coelacant1/BetaProtogen/Pictures/20210629_173443.jpg

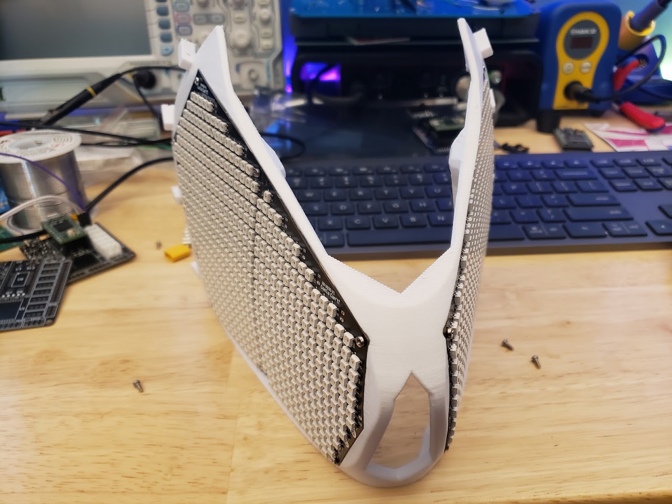
Pictures/20210629_173443.jpg
