coelacant1/BetaProtogen/Pictures/BottomLayer.png

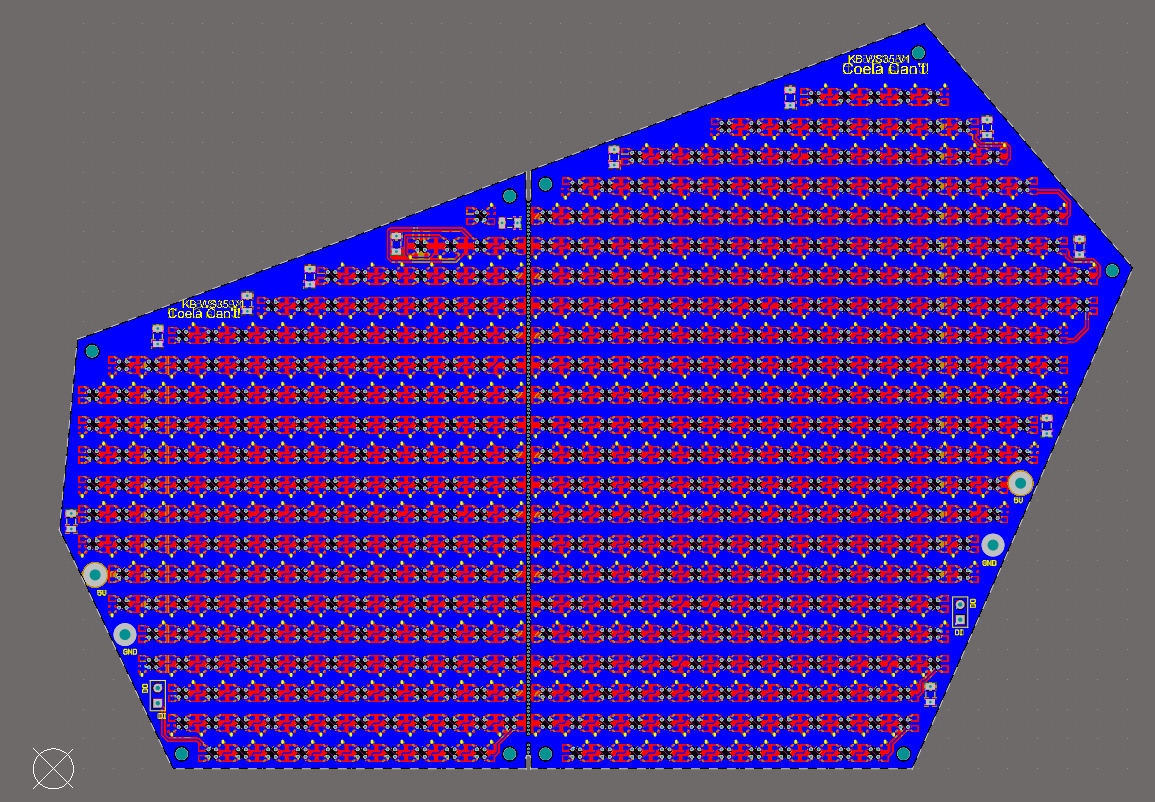
Pictures/BottomLayer.png
