coelacant1/BetaProtogen/Pictures/CoelaProtoPublicV1_WS35_blank.png

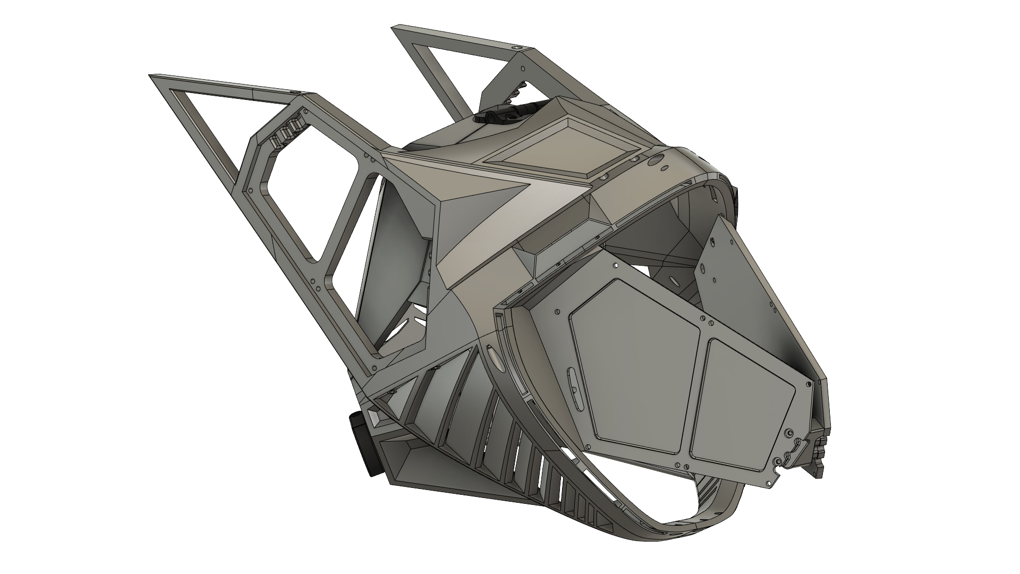
Pictures/CoelaProtoPublicV1_WS35_blank.png
