coelacant1/BetaProtogen/Pictures/CoelaProtoPublicV1_WS35_Bottom.png

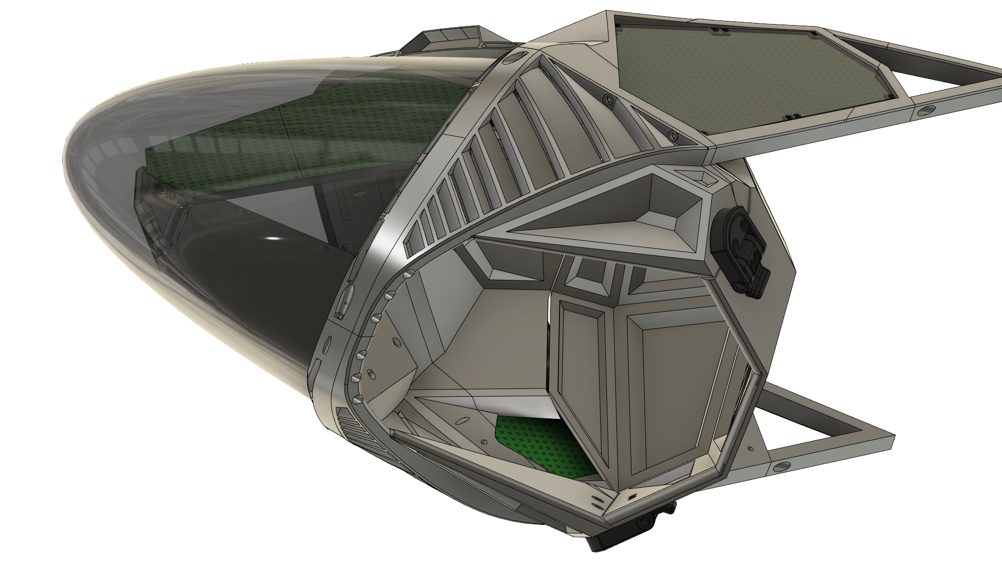
Pictures/CoelaProtoPublicV1_WS35_Bottom.png
