coelacant1/BetaProtogen/Pictures/CoelaProtoPublicV1_WS35_Full.png

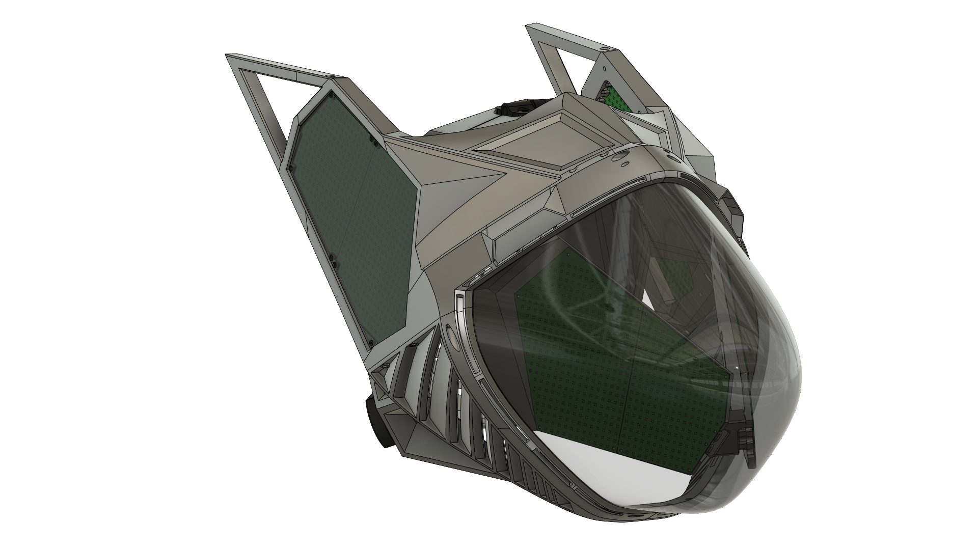
Pictures/CoelaProtoPublicV1_WS35_Full.png
