coelacant1/BetaProtogen/Pictures/CoelaProtoPublicV1_WS35_OpenBack.png

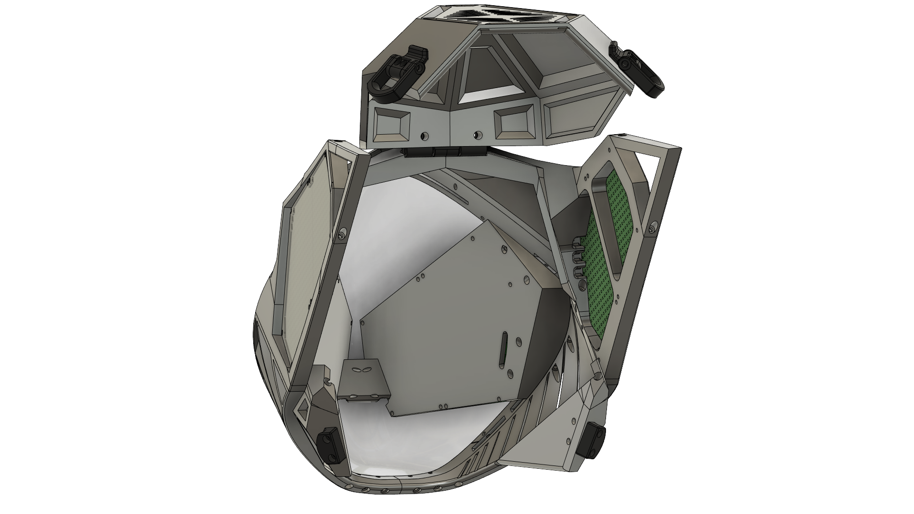
Pictures/CoelaProtoPublicV1_WS35_OpenBack.png
