coelacant1/BetaProtogen/Pictures/E_W8pO6XIAAdrPj.jpg

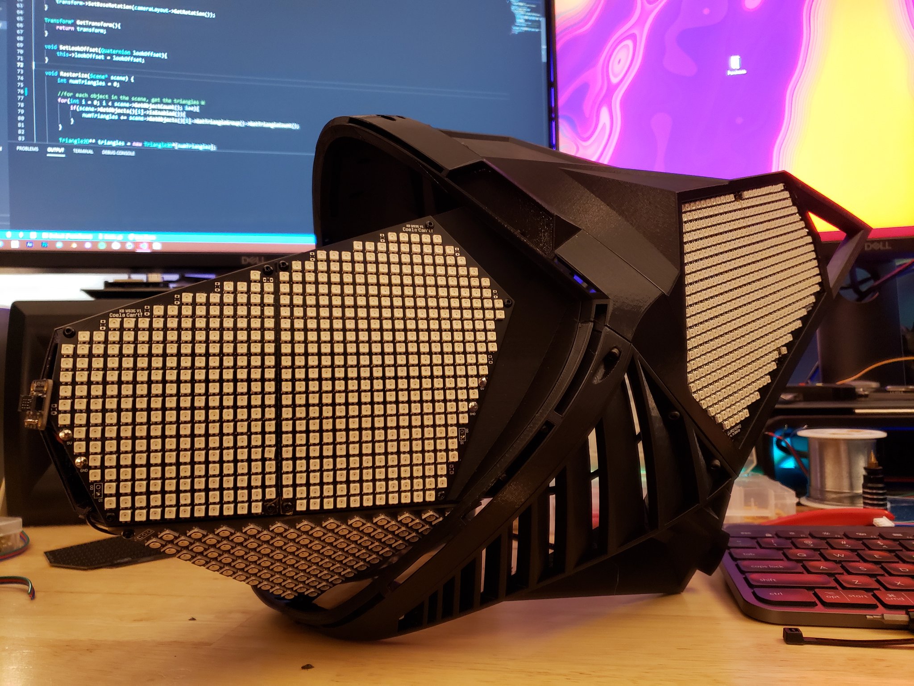
Pictures/E_W8pO6XIAAdrPj.jpg
