coelacant1/BetaProtogen/Pictures/FullHead.png

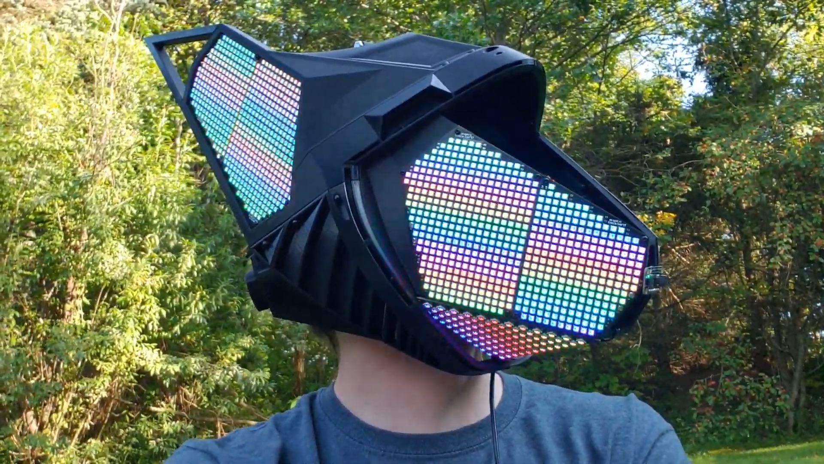
Pictures/FullHead.png
