coelacant1/BetaProtogen/Pictures/LED.png

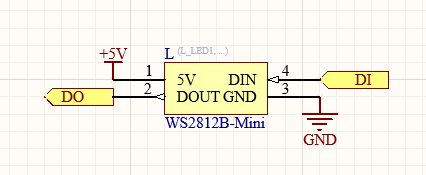
Pictures/LED.png
