coelacant1/BetaProtogen/Pictures/Thumbnail.png

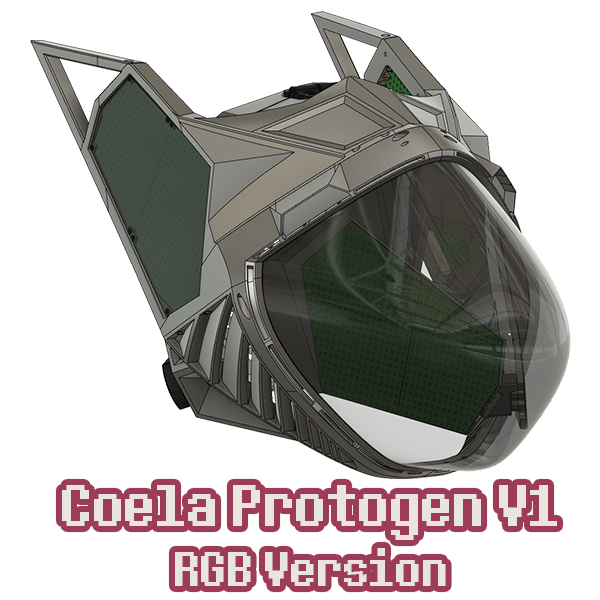
Pictures/Thumbnail.png
