coelacant1/BetaProtogen/Pictures/TopCopper.png

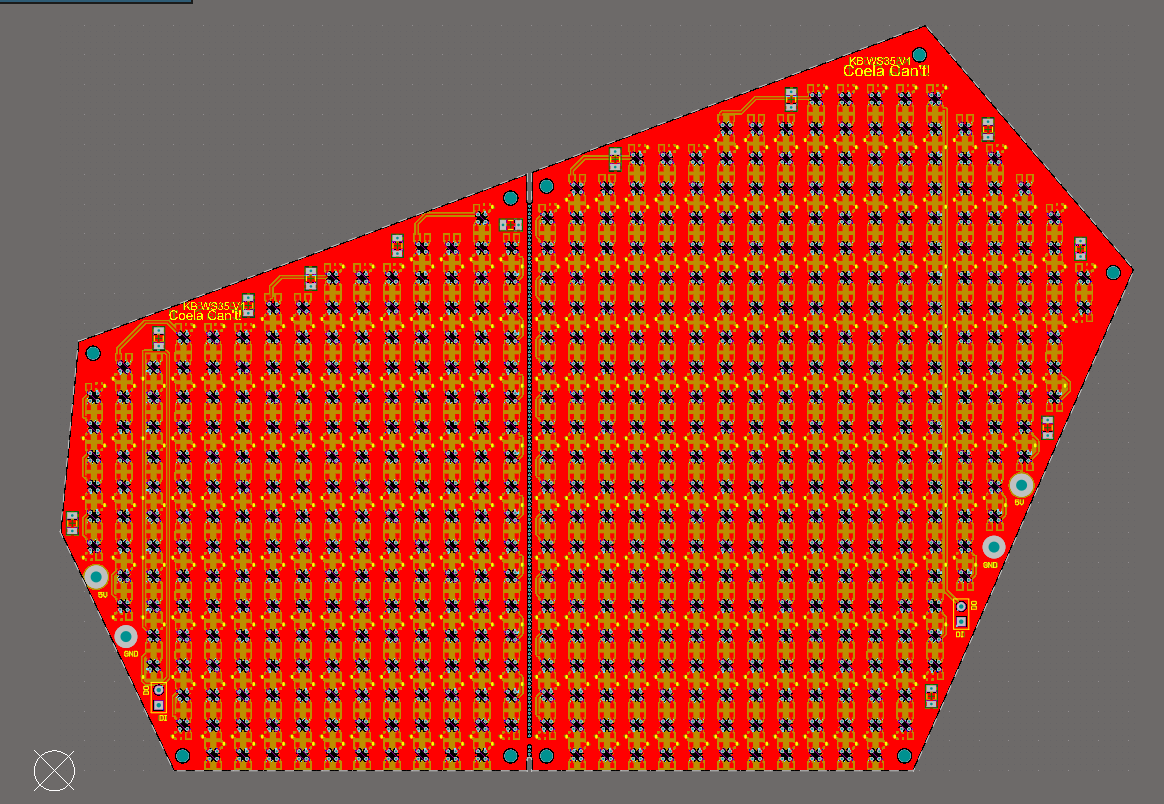
Pictures/TopCopper.png
