coelacant1/BetaProtogen/LED Mount WS35/WS35FlatMountRight_V1-0.stl

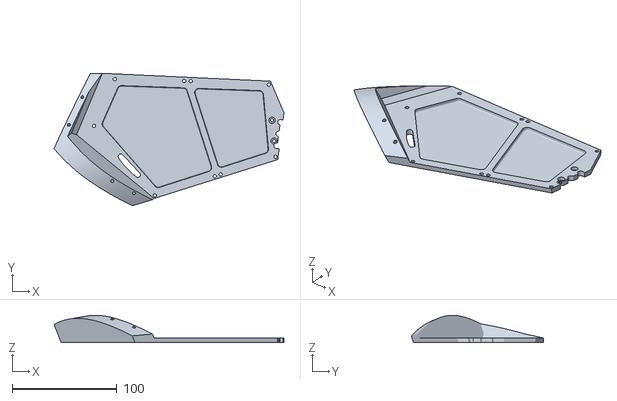
[picture p32: CAD file, 2023-06-26]
LED Mount WS35/WS35FlatMountRight_V1-0.stl
219.6 x 126.5 x 26.1
