coelacant1/BetaProtogen/Visor/Visor_V1-0.stl

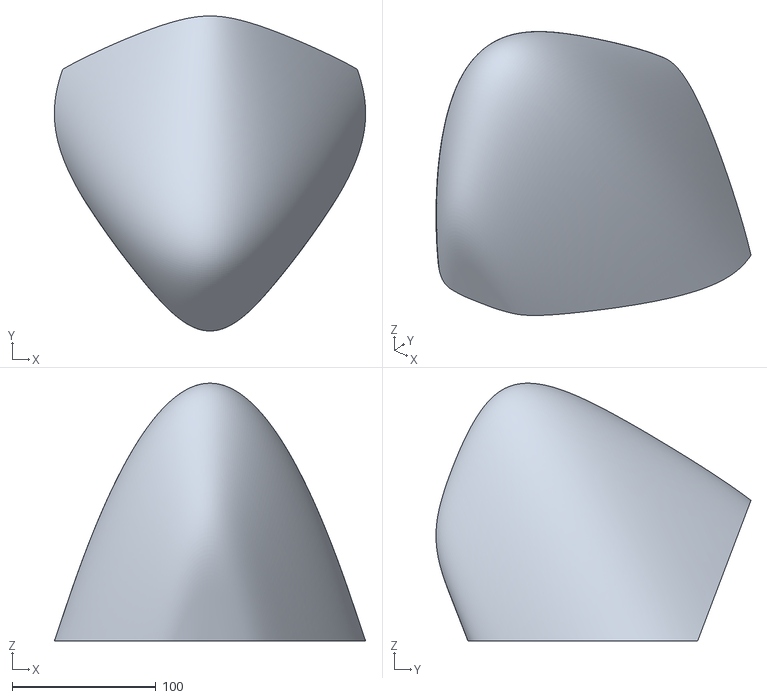
[picture p33: CAD file, 2023-06-26]
Visor/Visor_V1-0.stl
216.9 x 219.5 x 179.5
