coelacant1/BetaProtogen/VisorMount/BotVisorFrameMount_V1-0.stl

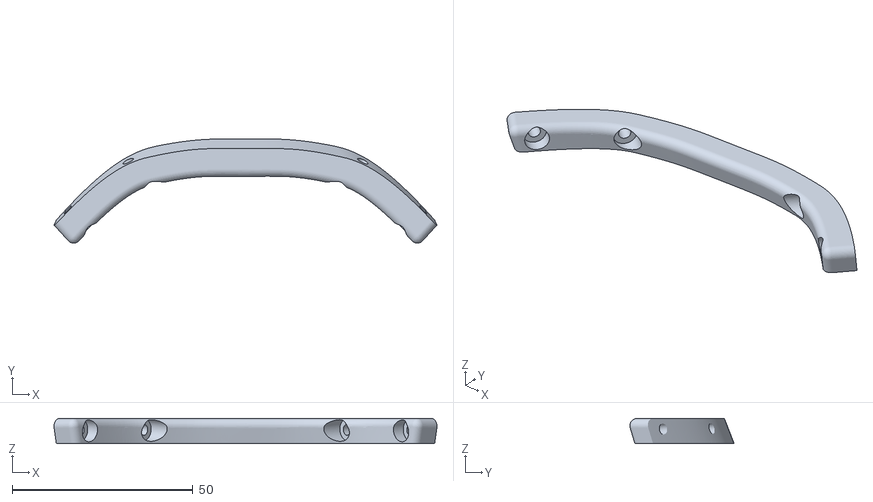
[picture p34: CAD file, 2023-06-26]
VisorMount/BotVisorFrameMount_V1-0.stl
106.0 x 28.9 x 6.94
