coelacant1/BetaProtogen/Frame/FrameForeheadL_V1-1.stl

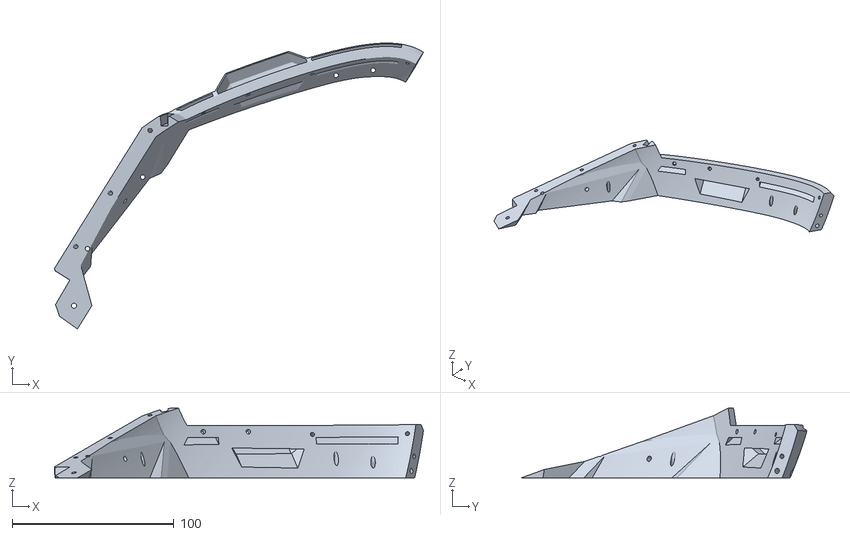
[picture p35: CAD file, 2023-06-26]
Frame/FrameForeheadL_V1-1.stl
228.0 x 176.6 x 43.2
