coelacant1/BetaProtogen/VisorMount/TopBackMagnet.stl

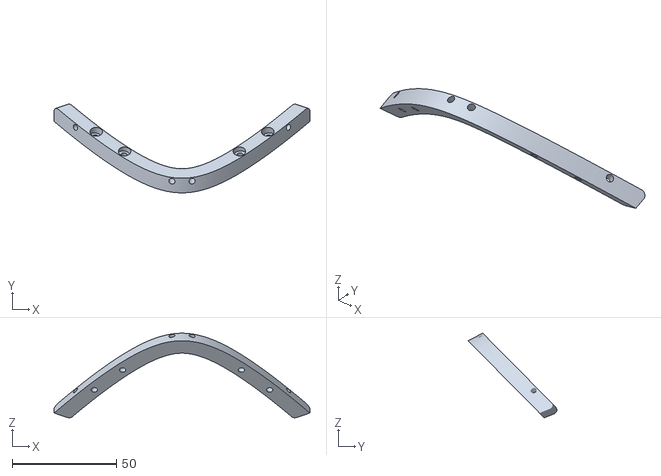
[picture p38: CAD file, 2023-06-26]
VisorMount/TopBackMagnet.stl
122.6 x 42.5 x 40.5
