coelacant1/BetaProtogen/Frame/FrameJawR_V1-1.stl

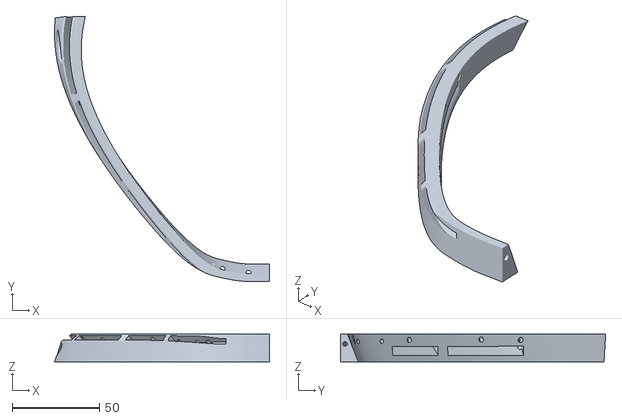
[picture p39: CAD file, 2023-06-26]
Frame/FrameJawR_V1-1.stl
123.0 x 151.8 x 15.8
