coelacant1/BetaProtogen/Latch/LatchRightMount_V1-0.stl

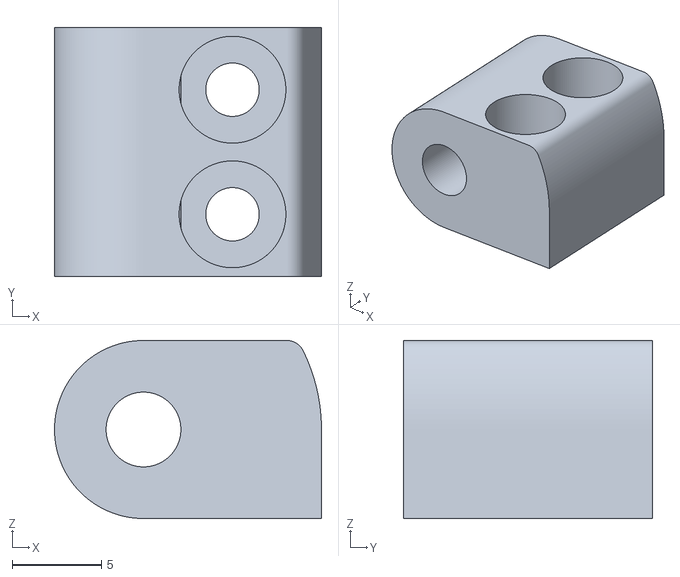
[picture p40: CAD file, 2023-06-26]
Latch/LatchRightMount_V1-0.stl
15.0 x 14.0 x 10.0
