coelacant1/BetaProtogen/LED Mount MAX7219/MAX7219BottomRight_V1-0.stl

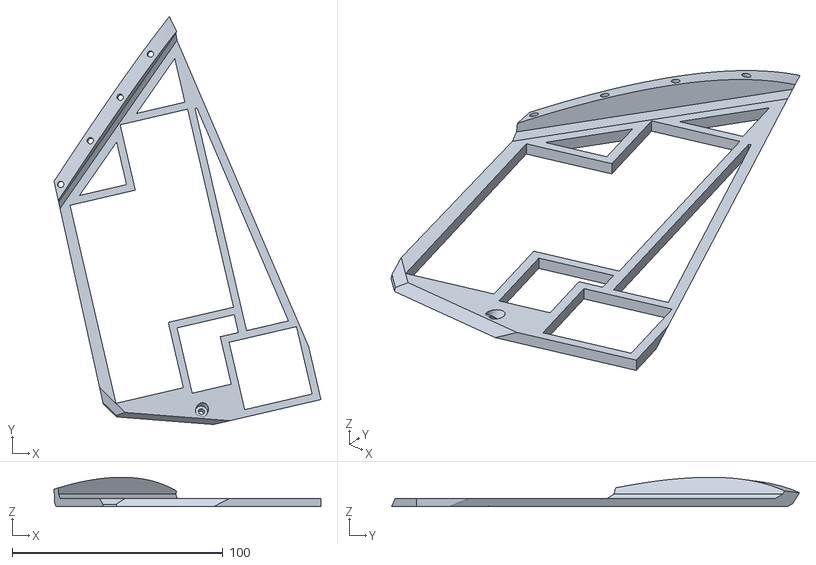
[picture p41: CAD file, 2023-06-26]
LED Mount MAX7219/MAX7219BottomRight_V1-0.stl
126.6 x 193.4 x 14.0
