coelacant1/BetaProtogen/LED Mount WS35/WS35BendMount_V1-0.stl

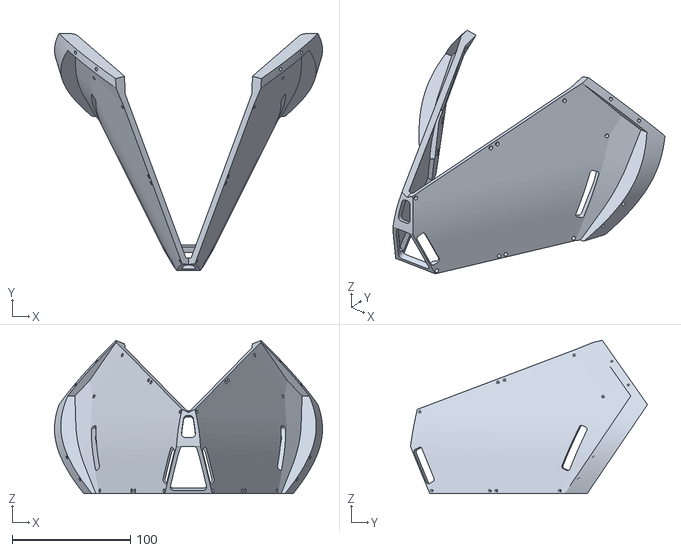
[picture p42: CAD file, 2023-06-26]
LED Mount WS35/WS35BendMount_V1-0.stl
226.4 x 200.2 x 129.4
