coelacant1/BetaProtogen/Visor/VisorCoverBottom_V1-0.stl

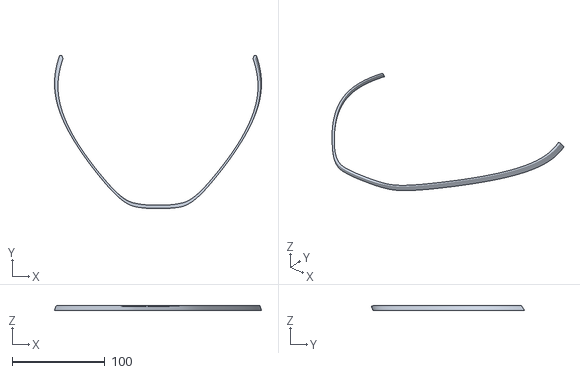
[picture p43: CAD file, 2023-06-26]
Visor/VisorCoverBottom_V1-0.stl
222.6 x 164.7 x 5.00
