coelacant1/BetaProtogen/VisorMount/TopVisorFrameMount_V1-0.stl

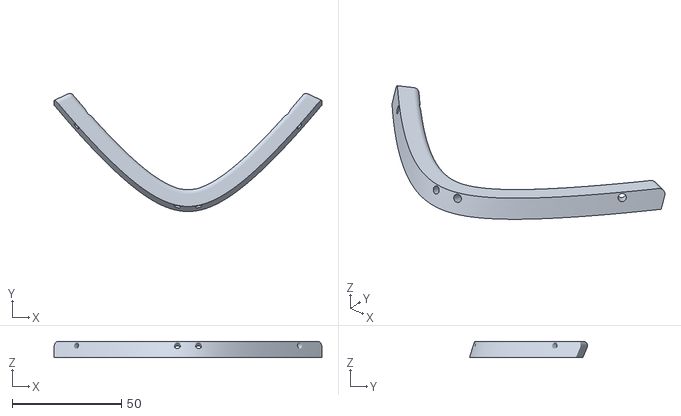
[picture p44: CAD file, 2023-06-26]
VisorMount/TopVisorFrameMount_V1-0.stl
122.6 x 54.0 x 7.54
