coelacant1/BetaProtogen/Frame/FrameForeheadR_V1-1.stl

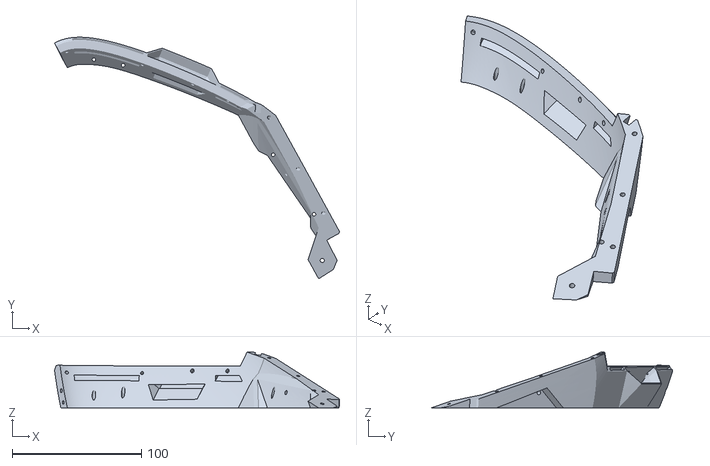
[picture p45: CAD file, 2023-06-26]
Frame/FrameForeheadR_V1-1.stl
220.4 x 186.8 x 43.2
