coelacant1/BetaProtogen/LED Mount MAX7219/MAX7219LEDConnector_V1-0.stl

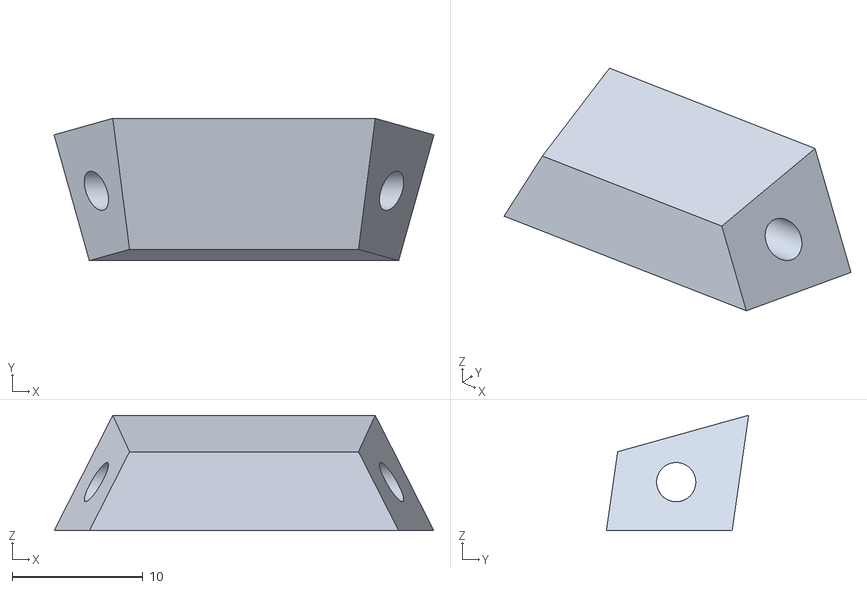
[picture p47: CAD file, 2023-06-26]
LED Mount MAX7219/MAX7219LEDConnector_V1-0.stl
29.1 x 10.9 x 8.84
