coelacant1/BetaProtogen/LED Mount WS35/WS35FlatMountConnector_V1-0.stl

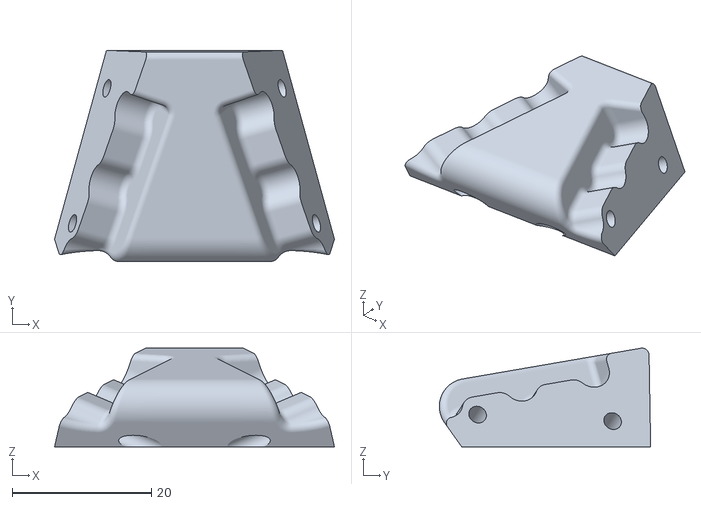
[picture p48: CAD file, 2023-06-26]
LED Mount WS35/WS35FlatMountConnector_V1-0.stl
40.2 x 30.3 x 14.2
