coelacant1/BetaProtogen/Visor/BuckTopLeft_V3-0.stl

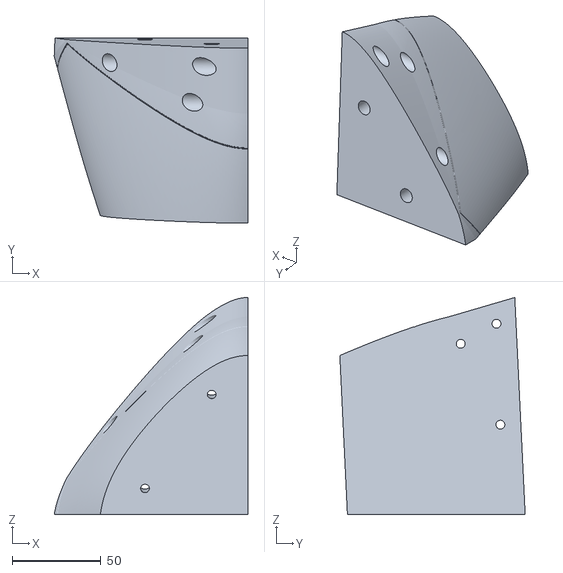
[picture p49: CAD file, 2023-06-26]
Visor/BuckTopLeft_V3-0.stl
109.0 x 104.4 x 122.2
