coelacant1/BetaProtogen/VisorMount/BotVisorMagnetMount_V1-0.stl

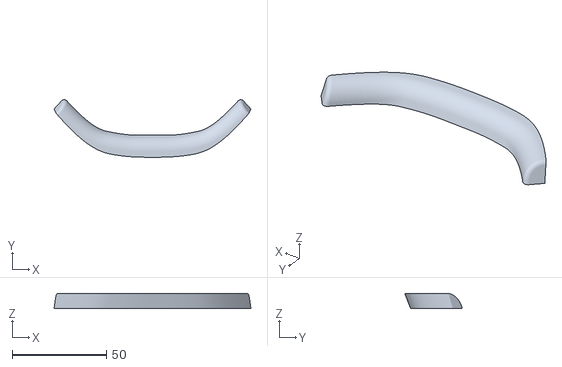
[picture p50: CAD file, 2023-06-26]
VisorMount/BotVisorMagnetMount_V1-0.stl
104.7 x 30.6 x 8.06
