coelacant1/BetaProtogen/VisorMount/BotBackMagnet.stl

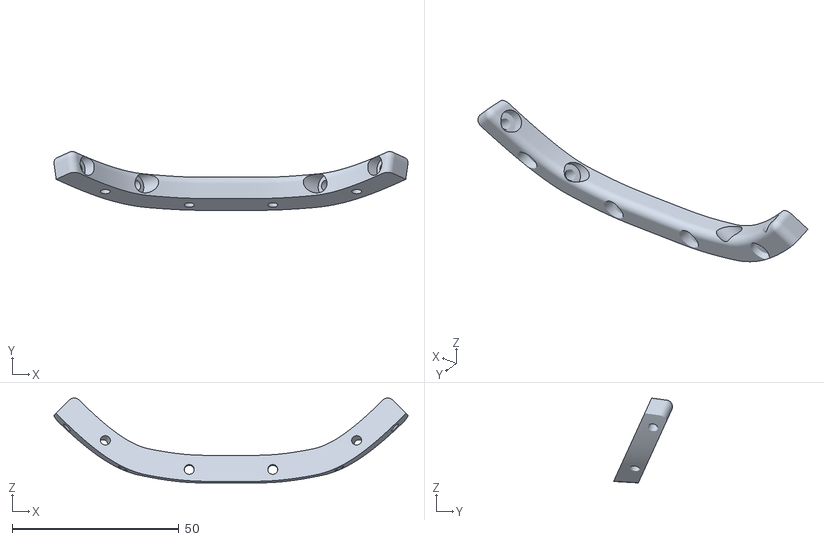
[picture p52: CAD file, 2023-06-26]
VisorMount/BotBackMagnet.stl
106.0 x 17.7 x 25.4
