coelacant1/BetaProtogen/LED Mount MAX7219/MAX7219LEDEarMountRight_V1-0.stl

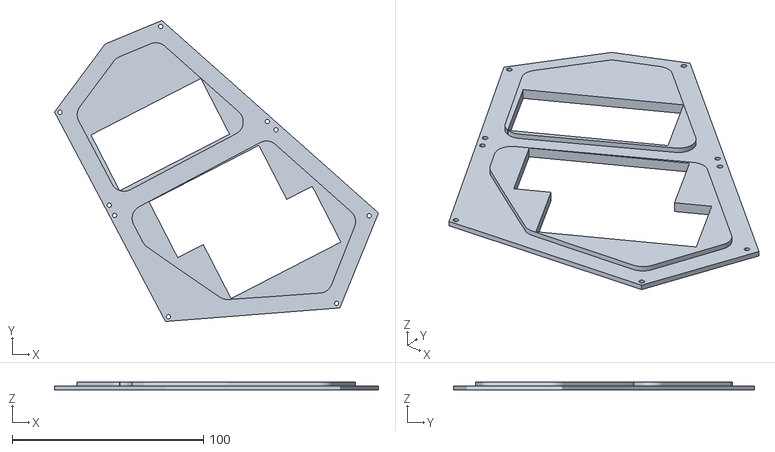
[picture p53: CAD file, 2023-06-26]
LED Mount MAX7219/MAX7219LEDEarMountRight_V1-0.stl
169.4 x 157.4 x 4.00
