coelacant1/BetaProtogen/Visor/VisorCoverTop_V1-0.stl

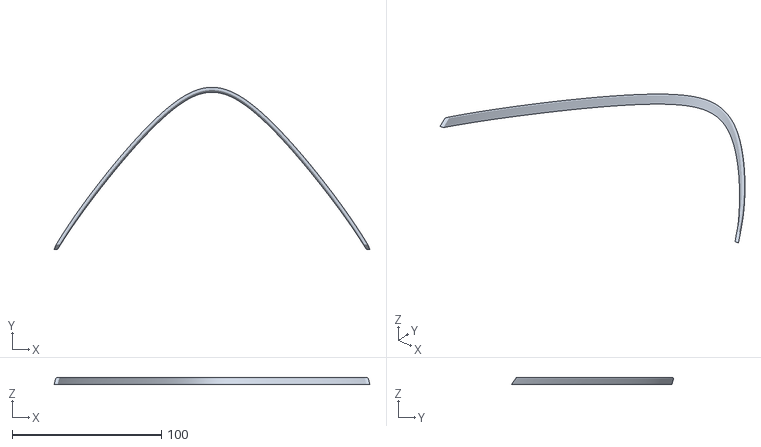
[picture p54: CAD file, 2023-06-26]
Visor/VisorCoverTop_V1-0.stl
211.7 x 108.7 x 5.00
