coelacant1/BetaProtogen/VisorMount/BotFrontMagnet.stl

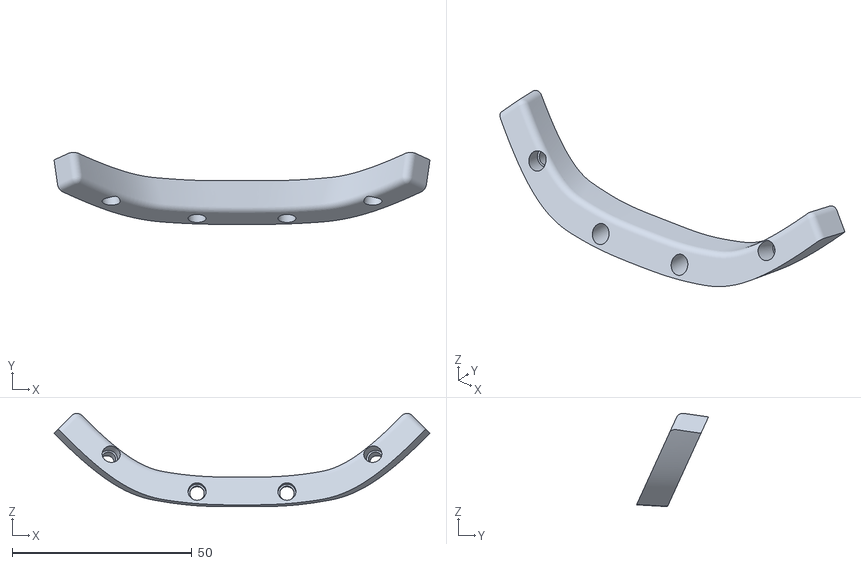
[picture p55: CAD file, 2023-06-26]
VisorMount/BotFrontMagnet.stl
104.7 x 20.1 x 26.0
