coelacant1/BetaProtogen/VisorMount/TopFrontMagnet.stl

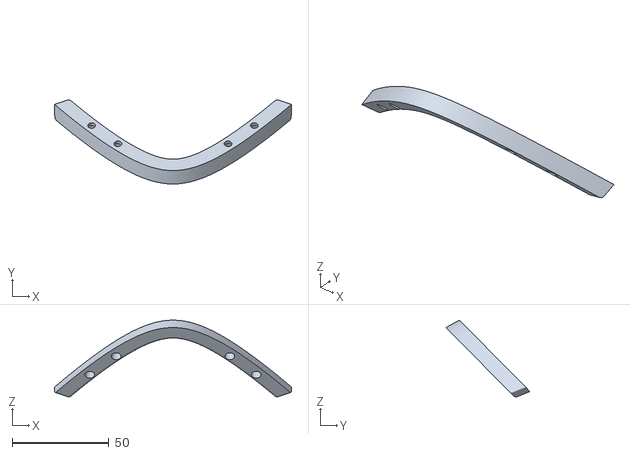
[picture p56: CAD file, 2023-06-26]
VisorMount/TopFrontMagnet.stl
122.5 x 43.4 x 39.7
